oballinger/ssymmank-lamp/models/assembly/_overlap_check.scad

// OVERLAP CHECK for assembly.scad -- renders ONLY the 3D intersection of each
// close mushroom pair. Red / non-empty STL = real physical intersection;
// "top level object is empty" / 0 facets = clean. Generated by build.py.
use <../mushrooms/mushroom_simple.scad>;
MUSH_SCALE = 0.85;
MUSH = [
    [[[-0.80902, -0.58779, 0.00000, 0.00000], [-0.30902, 0.42533, 0.85065, 162.64443], [-0.50000, 0.68819, -0.52573, -100.51979], [0.00000, 0.00000, 0.00000, 1.00000]], 112.00],
    [[[0.30902, -0.87934, -0.36231, -56.33897], [-0.50000, -0.47427, 0.72462, 112.67795], [-0.80902, -0.04276, -0.58623, -91.15838], [0.00000, 0.00000, 0.00000, 1.00000]], 70.00],
    [[[1.00000, 0.00000, 0.00000, 0.00000], [0.00000, -0.81015, 0.58623, 98.13448], [0.00000, -0.58623, -0.81015, -135.61852], [0.00000, 0.00000, 0.00000, 1.00000]], 84.00],
    [[[0.30902, 0.87934, 0.36231, 56.33897], [0.50000, -0.47427, 0.72462, 112.67795], [0.80902, -0.04276, -0.58623, -91.15838], [0.00000, 0.00000, 0.00000, 1.00000]], 70.00],
    [[[-0.80902, 0.54346, 0.22392, 37.48404], [0.30902, 0.06919, 0.94854, 158.78493], [0.50000, 0.83658, -0.22392, -37.48404], [0.00000, 0.00000, 0.00000, 1.00000]], 84.00],
    [[[-0.80902, -0.54346, -0.22392, -40.14867], [-0.30902, 0.06919, 0.94854, 170.07251], [-0.50000, 0.83658, -0.22392, -40.14867], [0.00000, 0.00000, 0.00000, 1.00000]], 98.00],
    [[[0.50000, 0.68819, -0.52573, -100.51979], [-0.80902, 0.58779, 0.00000, 0.00000], [0.30902, 0.42533, 0.85065, 162.64443], [0.00000, 0.00000, 0.00000, 1.00000]], 112.00],
    [[[0.50000, 0.83658, -0.22392, -34.81940], [-0.80902, 0.54346, 0.22392, 34.81940], [0.30902, 0.06919, 0.94854, 147.49735], [0.00000, 0.00000, 0.00000, 1.00000]], 70.00],
    [[[-0.50000, 0.83658, -0.22392, -37.48404], [-0.80902, -0.54346, -0.22392, -37.48404], [-0.30902, 0.06919, 0.94854, 158.78493], [0.00000, 0.00000, 0.00000, 1.00000]], 84.00],
    [[[-0.80902, -0.04276, -0.58623, -91.15838], [0.30902, -0.87934, -0.36231, -56.33897], [-0.50000, -0.47427, 0.72462, 112.67795], [0.00000, 0.00000, 0.00000, 1.00000]], 70.00],
    [[[0.00000, -0.58623, -0.81015, -135.61852], [1.00000, 0.00000, 0.00000, 0.00000], [0.00000, -0.81015, 0.58623, 98.13448], [0.00000, 0.00000, 0.00000, 1.00000]], 84.00],
    [[[0.80902, -0.04276, -0.58623, -105.11059], [0.30902, 0.87934, 0.36231, 64.96192], [0.50000, -0.47427, 0.72462, 129.92384], [0.00000, 0.00000, 0.00000, 1.00000]], 98.00],
    [[[-0.86603, 0.50000, 0.00000, 0.00000], [-0.26287, -0.45530, 0.85065, 152.52169], [0.42533, 0.73669, 0.52573, 94.26359], [0.00000, 0.00000, 0.00000, 1.00000]], 98.00],
    [[[-1.00000, 0.00000, 0.00000, 0.00000], [0.00000, -0.81015, 0.58623, 98.13448], [0.00000, 0.58623, 0.81015, 135.61852], [0.00000, 0.00000, 0.00000, 1.00000]], 84.00],
    [[[-0.30902, -0.87934, -0.36231, -69.27339], [0.50000, -0.47427, 0.72462, 138.54678], [-0.80902, 0.04276, 0.58623, 112.08670], [0.00000, 0.00000, 0.00000, 1.00000]], 112.00],
    [[[0.80902, -0.54346, -0.22392, -34.81940], [0.30902, 0.06919, 0.94854, 147.49735], [-0.50000, -0.83658, 0.22392, 34.81940], [0.00000, 0.00000, 0.00000, 1.00000]], 70.00],
    [[[0.80902, 0.54346, 0.22392, 42.81331], [-0.30902, 0.06919, 0.94854, 181.36009], [0.50000, -0.83658, 0.22392, 42.81331], [0.00000, 0.00000, 0.00000, 1.00000]], 112.00],
    [[[-0.30902, 0.87934, 0.36231, 56.33897], [-0.50000, -0.47427, 0.72462, 112.67795], [0.80902, 0.04276, 0.58623, 91.15838], [0.00000, 0.00000, 0.00000, 1.00000]], 70.00],
    [[[0.00000, 0.85065, 0.52573, 106.77599], [1.00000, 0.00000, 0.00000, 0.00000], [0.00000, 0.52573, -0.85065, -172.76718], [0.00000, 0.00000, 0.00000, 1.00000]], 126.00],
    [[[0.00000, 0.58623, 0.81015, 125.97778], [1.00000, 0.00000, 0.00000, 0.00000], [0.00000, 0.81015, -0.58623, -91.15838], [0.00000, 0.00000, 0.00000, 1.00000]], 70.00],
    [[[-0.80902, 0.04276, 0.58623, 105.11059], [0.30902, 0.87934, 0.36231, 64.96192], [-0.50000, 0.47427, -0.72462, -129.92384], [0.00000, 0.00000, 0.00000, 1.00000]], 98.00],
    [[[-0.50000, -0.83658, 0.22392, 42.81331], [-0.80902, 0.54346, 0.22392, 42.81331], [-0.30902, -0.06919, -0.94854, -181.36009], [0.00000, 0.00000, 0.00000, 1.00000]], 112.00],
    [[[0.50000, -0.83658, 0.22392, 34.81940], [-0.80902, -0.54346, -0.22392, -34.81940], [0.30902, -0.06919, -0.94854, -147.49735], [0.00000, 0.00000, 0.00000, 1.00000]], 70.00],
    [[[0.80902, 0.04276, 0.58623, 98.13448], [0.30902, -0.87934, -0.36231, -60.65045], [0.50000, 0.47427, -0.72462, -121.30089], [0.00000, 0.00000, 0.00000, 1.00000]], 84.00],
    [[[0.50000, -0.68819, 0.52573, 106.77599], [0.80902, 0.58779, 0.00000, 0.00000], [-0.30902, 0.42533, 0.85065, 172.76718], [0.00000, 0.00000, 0.00000, 1.00000]], 126.00],
    [[[0.50000, -0.83658, 0.22392, 40.14867], [0.80902, 0.54346, 0.22392, 40.14867], [-0.30902, 0.06919, 0.94854, 170.07251], [0.00000, 0.00000, 0.00000, 1.00000]], 98.00],
    [[[0.80902, 0.04276, 0.58623, 112.08670], [-0.30902, 0.87934, 0.36231, 69.27339], [-0.50000, -0.47427, 0.72462, 138.54678], [0.00000, 0.00000, 0.00000, 1.00000]], 112.00],
    [[[0.00000, 0.58623, 0.81015, 125.97778], [-1.00000, 0.00000, 0.00000, 0.00000], [0.00000, -0.81015, 0.58623, 91.15838], [0.00000, 0.00000, 0.00000, 1.00000]], 70.00],
    [[[-0.80902, 0.04276, 0.58623, 98.13448], [-0.30902, -0.87934, -0.36231, -60.65045], [0.50000, -0.47427, 0.72462, 121.30089], [0.00000, 0.00000, 0.00000, 1.00000]], 84.00],
    [[[-0.50000, -0.83658, 0.22392, 42.81331], [0.80902, -0.54346, -0.22392, -42.81331], [0.30902, 0.06919, 0.94854, 181.36009], [0.00000, 0.00000, 0.00000, 1.00000]], 112.00],
    [[[-0.00000, -0.85065, -0.52573, -100.51979], [-1.00000, 0.00000, 0.00000, 0.00000], [0.00000, 0.52573, -0.85065, -162.64443], [0.00000, 0.00000, 0.00000, 1.00000]], 112.00],
    [[[-0.00000, -0.58623, -0.81015, -125.97778], [-1.00000, 0.00000, 0.00000, 0.00000], [0.00000, 0.81015, -0.58623, -91.15838], [0.00000, 0.00000, 0.00000, 1.00000]], 70.00],
    [[[0.80902, -0.04276, -0.58623, -98.13448], [-0.30902, -0.87934, -0.36231, -60.65045], [-0.50000, 0.47427, -0.72462, -121.30089], [0.00000, 0.00000, 0.00000, 1.00000]], 84.00],
    [[[0.50000, 0.83658, -0.22392, -40.14867], [0.80902, -0.54346, -0.22392, -40.14867], [-0.30902, -0.06919, -0.94854, -170.07251], [0.00000, 0.00000, 0.00000, 1.00000]], 98.00],
    [[[-0.50000, 0.83658, -0.22392, -45.47794], [0.80902, 0.54346, 0.22392, 45.47794], [0.30902, -0.06919, -0.94854, -192.64767], [0.00000, 0.00000, 0.00000, 1.00000]], 126.00],
    [[[-0.80902, -0.04276, -0.58623, -105.11059], [-0.30902, 0.87934, 0.36231, 64.96192], [0.50000, 0.47427, -0.72462, -129.92384], [0.00000, 0.00000, 0.00000, 1.00000]], 98.00],
    [[[0.80902, 0.58779, 0.00000, 0.00000], [0.30902, -0.42533, -0.85065, -172.76718], [-0.50000, 0.68819, -0.52573, -106.77599], [0.00000, 0.00000, 0.00000, 1.00000]], 126.00],
    [[[-0.30902, 0.87934, 0.36231, 64.96192], [0.50000, 0.47427, -0.72462, -129.92384], [-0.80902, -0.04276, -0.58623, -105.11059], [0.00000, 0.00000, 0.00000, 1.00000]], 98.00],
    [[[-1.00000, 0.00000, 0.00000, 0.00000], [0.00000, 0.81015, -0.58623, -112.08670], [-0.00000, -0.58623, -0.81015, -154.90001], [0.00000, 0.00000, 0.00000, 1.00000]], 112.00],
    [[[-0.30902, -0.87934, -0.36231, -56.33897], [-0.50000, 0.47427, -0.72462, -112.67795], [0.80902, -0.04276, -0.58623, -91.15838], [0.00000, 0.00000, 0.00000, 1.00000]], 70.00],
    [[[0.80902, -0.54346, -0.22392, -37.48404], [-0.30902, -0.06919, -0.94854, -158.78493], [0.50000, 0.83658, -0.22392, -37.48404], [0.00000, 0.00000, 0.00000, 1.00000]], 84.00],
    [[[0.80902, 0.54346, 0.22392, 42.81331], [0.30902, -0.06919, -0.94854, -181.36009], [-0.50000, 0.83658, -0.22392, -42.81331], [0.00000, 0.00000, 0.00000, 1.00000]], 112.00],
    [[[0.86603, -0.50000, 0.00000, 0.00000], [0.26287, 0.45530, -0.85065, -142.39895], [0.42533, 0.73669, 0.52573, 88.00739], [0.00000, 0.00000, 0.00000, 1.00000]], 84.00],
    [[[1.00000, 0.00000, 0.00000, 0.00000], [0.00000, 0.81015, -0.58623, -105.11059], [0.00000, 0.58623, 0.81015, 145.25926], [0.00000, 0.00000, 0.00000, 1.00000]], 98.00],
    [[[0.30902, 0.87934, 0.36231, 56.33897], [-0.50000, 0.47427, -0.72462, -112.67795], [-0.80902, 0.04276, 0.58623, 91.15838], [0.00000, 0.00000, 0.00000, 1.00000]], 70.00],
    [[[-0.80902, 0.54346, 0.22392, 40.14867], [-0.30902, -0.06919, -0.94854, -170.07251], [-0.50000, -0.83658, 0.22392, 40.14867], [0.00000, 0.00000, 0.00000, 1.00000]], 98.00],
    [[[-0.80902, -0.54346, -0.22392, -34.81940], [0.30902, -0.06919, -0.94854, -147.49735], [0.50000, -0.83658, 0.22392, 34.81940], [0.00000, 0.00000, 0.00000, 1.00000]], 70.00],
    [[[0.30902, -0.87934, -0.36231, -69.27339], [0.50000, 0.47427, -0.72462, -138.54678], [0.80902, 0.04276, 0.58623, 112.08670], [0.00000, 0.00000, 0.00000, 1.00000]], 112.00],
    [[[0.50000, 0.16246, 0.85065, 132.27620], [-0.80902, -0.26287, 0.52573, 81.75119], [0.30902, -0.95106, 0.00000, 0.00000], [0.00000, 0.00000, 0.00000, 1.00000]], 70.00],
    [[[-0.50000, -0.47427, 0.72462, 121.30089], [0.80902, 0.04276, 0.58623, 98.13448], [-0.30902, 0.87934, 0.36231, 60.65045], [0.00000, 0.00000, 0.00000, 1.00000]], 84.00],
    [[[0.00000, -0.81015, 0.58623, 105.11059], [0.00000, 0.58623, 0.81015, 145.25926], [-1.00000, 0.00000, 0.00000, 0.00000], [0.00000, 0.00000, 0.00000, 1.00000]], 98.00],
    [[[0.50000, -0.47427, 0.72462, 138.54678], [-0.80902, 0.04276, 0.58623, 112.08670], [-0.30902, -0.87934, -0.36231, -69.27339], [0.00000, 0.00000, 0.00000, 1.00000]], 112.00],
    [[[0.30902, 0.06919, 0.94854, 158.78493], [-0.50000, -0.83658, 0.22392, 37.48404], [0.80902, -0.54346, -0.22392, -37.48404], [0.00000, 0.00000, 0.00000, 1.00000]], 84.00],
    [[[-0.30902, 0.06919, 0.94854, 170.07251], [0.50000, -0.83658, 0.22392, 40.14867], [0.80902, 0.54346, 0.22392, 40.14867], [0.00000, 0.00000, 0.00000, 1.00000]], 98.00],
    [[[0.51424, -0.10931, -0.85065, -132.27620], [-0.83206, 0.17686, -0.52573, -81.75119], [0.20791, 0.97815, 0.00000, 0.00000], [0.00000, 0.00000, 0.00000, 1.00000]], 70.00],
    [[[0.00000, 0.81015, -0.58623, -105.11059], [-0.00000, -0.58623, -0.81015, -145.25926], [-1.00000, 0.00000, 0.00000, 0.00000], [0.00000, 0.00000, 0.00000, 1.00000]], 98.00],
    [[[-0.50000, 0.47427, -0.72462, -138.54678], [0.80902, -0.04276, -0.58623, -112.08670], [-0.30902, -0.87934, -0.36231, -69.27339], [0.00000, 0.00000, 0.00000, 1.00000]], 112.00],
    [[[-0.30902, -0.06919, -0.94854, -170.07251], [0.50000, 0.83658, -0.22392, -40.14867], [0.80902, -0.54346, -0.22392, -40.14867], [0.00000, 0.00000, 0.00000, 1.00000]], 98.00],
    [[[0.30902, -0.06919, -0.94854, -181.36009], [-0.50000, 0.83658, -0.22392, -42.81331], [0.80902, 0.54346, 0.22392, 42.81331], [0.00000, 0.00000, 0.00000, 1.00000]], 112.00],
    [[[0.50000, 0.47427, -0.72462, -147.16972], [-0.80902, -0.04276, -0.58623, -119.06281], [-0.30902, 0.87934, 0.36231, 73.58486], [0.00000, 0.00000, 0.00000, 1.00000]], 126.00],
    [[[-0.50000, 0.16246, -0.85065, -152.52169], [-0.80902, 0.26287, 0.52573, 94.26359], [0.30902, 0.95106, 0.00000, 0.00000], [0.00000, 0.00000, 0.00000, 1.00000]], 98.00],
    [[[-0.50000, 0.47427, -0.72462, -147.16972], [-0.80902, 0.04276, 0.58623, 119.06281], [0.30902, 0.87934, 0.36231, 73.58486], [0.00000, 0.00000, 0.00000, 1.00000]], 126.00],
    [[[-0.30902, -0.06919, -0.94854, -147.49735], [-0.50000, -0.83658, 0.22392, 34.81940], [-0.80902, 0.54346, 0.22392, 34.81940], [0.00000, 0.00000, 0.00000, 1.00000]], 70.00],
    [[[0.30902, -0.06919, -0.94854, -158.78493], [0.50000, -0.83658, 0.22392, 37.48404], [-0.80902, -0.54346, -0.22392, -37.48404], [0.00000, 0.00000, 0.00000, 1.00000]], 84.00],
    [[[0.50000, 0.47427, -0.72462, -138.54678], [0.80902, 0.04276, 0.58623, 112.08670], [0.30902, -0.87934, -0.36231, -69.27339], [0.00000, 0.00000, 0.00000, 1.00000]], 112.00],
    [[[0.00000, 0.81015, -0.58623, -98.13448], [0.00000, 0.58623, 0.81015, 135.61852], [1.00000, 0.00000, 0.00000, 0.00000], [0.00000, 0.00000, 0.00000, 1.00000]], 84.00],
    [[[0.35178, -0.39069, 0.85065, 132.27620], [0.56920, -0.63216, -0.52573, -81.75119], [0.74314, 0.66913, 0.00000, 0.00000], [0.00000, 0.00000, 0.00000, 1.00000]], 70.00],
    [[[0.30902, 0.06919, 0.94854, 192.64767], [0.50000, 0.83658, -0.22392, -45.47794], [-0.80902, 0.54346, 0.22392, 45.47794], [0.00000, 0.00000, 0.00000, 1.00000]], 126.00],
    [[[-0.30902, 0.06919, 0.94854, 181.36009], [-0.50000, 0.83658, -0.22392, -42.81331], [-0.80902, -0.54346, -0.22392, -42.81331], [0.00000, 0.00000, 0.00000, 1.00000]], 112.00],
    [[[-0.50000, -0.47427, 0.72462, 147.16972], [-0.80902, -0.04276, -0.58623, -119.06281], [0.30902, -0.87934, -0.36231, -73.58486], [0.00000, 0.00000, 0.00000, 1.00000]], 126.00],
    [[[0.00000, -0.81015, 0.58623, 98.13448], [0.00000, -0.58623, -0.81015, -135.61852], [1.00000, 0.00000, 0.00000, 0.00000], [0.00000, 0.00000, 0.00000, 1.00000]], 84.00],
    [[[0.50000, -0.47427, 0.72462, 138.54678], [0.80902, -0.04276, -0.58623, -112.08670], [0.30902, 0.87934, 0.36231, 69.27339], [0.00000, 0.00000, 0.00000, 1.00000]], 112.00]
];
PAIRS = [
    [0, 5],
    [1, 2],
    [1, 65],
    [2, 3],
    [2, 20],
    [2, 35],
    [3, 4],
    [4, 5],
    [4, 15],
    [6, 11],
    [7, 8],
    [7, 13],
    [8, 9],
    [8, 25],
    [9, 10],
    [10, 11],
    [10, 62],
    [11, 13],
    [12, 13],
    [12, 14],
    [12, 15],
    [12, 16],
    [12, 17],
    [13, 17],
    [15, 65],
    [17, 49],
    [19, 23],
    [19, 52],
    [20, 52],
    [22, 23],
    [27, 28],
    [27, 49],
    [28, 43],
    [28, 44],
    [30, 33],
    [30, 34],
    [30, 35],
    [31, 32],
    [31, 63],
    [32, 33],
    [32, 39],
    [32, 57],
    [35, 63],
    [37, 70],
    [39, 40],
    [40, 45],
    [40, 46],
    [42, 43],
    [42, 44],
    [42, 45],
    [42, 46],
    [42, 47],
    [44, 70],
    [48, 49],
    [48, 50],
    [48, 51],
    [48, 52],
    [48, 53],
    [49, 50],
    [49, 53],
    [52, 53],
    [54, 55],
    [54, 56],
    [54, 57],
    [54, 58],
    [54, 59],
    [60, 61],
    [60, 62],
    [60, 63],
    [60, 64],
    [60, 65],
    [62, 63],
    [66, 67],
    [66, 68],
    [66, 69],
    [66, 70],
    [66, 71]
];
module one(i){ multmatrix(MUSH[i][0]) scale(MUSH_SCALE) mushroom(MUSH[i][1], paint=false); }
color("red") for (p = PAIRS) intersection(){ one(p[0]); one(p[1]); }
