oballinger/ssymmank-lamp/models/frame/stars_assembly.scad

// Ssymmank lamp -- FIT CHECK: 12 star tiles + 60 connectors = full frame.
// Modules/params (incl. the kink welds) come from star.scad, so edits there
// propagate here -- this file only carries the world placements.

include <star.scad>
SHOW_STAR = false;   // library mode: don't draw the lone star tile

PLACE_M = [
    [[-0.58779, 0.80902, 0.00000, 0.00000], [0.42533, 0.30902, 0.85065, 85.06508], [0.68819, 0.50000, -0.52573, -52.57311], [0.00000, 0.00000, 0.00000, 1.00000]],
    [[0.68819, -0.50000, -0.52573, -52.57311], [0.58779, 0.80902, 0.00000, 0.00000], [0.42533, -0.30902, 0.85065, 85.06508], [0.00000, 0.00000, 0.00000, 1.00000]],
    [[0.00000, 1.00000, 0.00000, 0.00000], [-0.52573, 0.00000, 0.85065, 85.06508], [0.85065, -0.00000, 0.52573, 52.57311], [0.00000, 0.00000, 0.00000, 1.00000]],
    [[0.85065, 0.00000, 0.52573, 52.57311], [0.00000, -1.00000, 0.00000, 0.00000], [0.52573, 0.00000, -0.85065, -85.06508], [0.00000, 0.00000, 0.00000, 1.00000]],
    [[-0.68819, -0.50000, 0.52573, 52.57311], [0.58779, -0.80902, 0.00000, 0.00000], [0.42533, 0.30902, 0.85065, 85.06508], [0.00000, 0.00000, 0.00000, 1.00000]],
    [[-0.85065, 0.00000, -0.52573, -52.57311], [0.00000, 1.00000, 0.00000, 0.00000], [0.52573, 0.00000, -0.85065, -85.06508], [0.00000, 0.00000, 0.00000, 1.00000]],
    [[0.58779, -0.80902, 0.00000, 0.00000], [-0.42533, -0.30902, -0.85065, -85.06508], [0.68819, 0.50000, -0.52573, -52.57311], [0.00000, 0.00000, 0.00000, 1.00000]],
    [[0.00000, -1.00000, 0.00000, 0.00000], [0.52573, 0.00000, -0.85065, -85.06508], [0.85065, 0.00000, 0.52573, 52.57311], [0.00000, 0.00000, 0.00000, 1.00000]],
    [[-0.16246, 0.50000, 0.85065, 85.06508], [0.26287, -0.80902, 0.52573, 52.57311], [0.95106, 0.30902, 0.00000, 0.00000], [0.00000, 0.00000, 0.00000, 1.00000]],
    [[0.16246, -0.50000, -0.85065, -85.06508], [-0.26287, 0.80902, -0.52573, -52.57311], [0.95106, 0.30902, 0.00000, 0.00000], [0.00000, 0.00000, 0.00000, 1.00000]],
    [[0.16246, 0.50000, -0.85065, -85.06508], [0.26287, 0.80902, 0.52573, 52.57311], [0.95106, -0.30902, 0.00000, 0.00000], [0.00000, 0.00000, 0.00000, 1.00000]],
    [[-0.16246, -0.50000, 0.85065, 85.06508], [-0.26287, -0.80902, -0.52573, -52.57311], [0.95106, -0.30902, 0.00000, 0.00000], [0.00000, 0.00000, 0.00000, 1.00000]]
];
CONN_M = [
    [[0.00000, 0.22975, -0.97325, -94.85360], [1.00000, 0.00000, 0.00000, 0.00000], [0.00000, -0.97325, -0.22975, -22.39190], [0.00000, 0.00000, 0.00000, 1.00000]],
    [[0.30902, 0.30075, -0.90225, -87.93412], [0.50000, -0.85837, -0.11488, -11.19595], [-0.80902, -0.41563, -0.41563, -40.50732], [0.00000, 0.00000, 0.00000, 1.00000]],
    [[0.00000, -0.22975, -0.97325, -94.85360], [1.00000, 0.00000, 0.00000, 0.00000], [0.00000, -0.97325, 0.22975, 22.39190], [0.00000, 0.00000, 0.00000, 1.00000]],
    [[0.30902, -0.30075, -0.90225, -87.93412], [0.50000, 0.85837, -0.11488, -11.19595], [0.80902, -0.41563, 0.41563, 40.50732], [0.00000, 0.00000, 0.00000, 1.00000]],
    [[0.30902, -0.30075, -0.90225, -87.93412], [-0.50000, -0.85837, 0.11488, 11.19595], [-0.80902, 0.41563, -0.41563, -40.50732], [0.00000, 0.00000, 0.00000, 1.00000]],
    [[0.30902, 0.30075, -0.90225, -87.93412], [-0.50000, 0.85837, 0.11488, 11.19595], [0.80902, 0.41563, 0.41563, 40.50732], [0.00000, 0.00000, 0.00000, 1.00000]],
    [[0.30902, 0.67250, -0.67250, -65.54223], [0.50000, -0.71638, -0.48662, -47.42680], [-0.80902, -0.18587, -0.55762, -54.34628], [0.00000, 0.00000, 0.00000, 1.00000]],
    [[0.80902, 0.18587, -0.55762, -54.34628], [-0.30902, -0.67250, -0.67250, -65.54223], [-0.50000, 0.71638, -0.48662, -47.42680], [0.00000, 0.00000, 0.00000, 1.00000]],
    [[0.30902, -0.67250, -0.67250, -65.54223], [0.50000, 0.71638, -0.48662, -47.42680], [0.80902, -0.18587, 0.55762, 54.34628], [0.00000, 0.00000, 0.00000, 1.00000]],
    [[0.80902, -0.18587, -0.55762, -54.34628], [-0.30902, 0.67250, -0.67250, -65.54223], [0.50000, 0.71638, 0.48662, 47.42680], [0.00000, 0.00000, 0.00000, 1.00000]],
    [[0.30902, -0.67250, -0.67250, -65.54223], [-0.50000, -0.71638, 0.48662, 47.42680], [-0.80902, 0.18587, -0.55762, -54.34628], [0.00000, 0.00000, 0.00000, 1.00000]],
    [[0.80902, -0.18587, -0.55762, -54.34628], [0.30902, -0.67250, 0.67250, 65.54223], [-0.50000, -0.71638, -0.48662, -47.42680], [0.00000, 0.00000, 0.00000, 1.00000]],
    [[0.30902, 0.67250, -0.67250, -65.54223], [-0.50000, 0.71638, 0.48662, 47.42680], [0.80902, 0.18587, 0.55762, 54.34628], [0.00000, 0.00000, 0.00000, 1.00000]],
    [[0.80902, 0.18587, -0.55762, -54.34628], [0.30902, 0.67250, 0.67250, 65.54223], [0.50000, -0.71638, 0.48662, 47.42680], [0.00000, 0.00000, 0.00000, 1.00000]],
    [[0.80902, 0.41563, -0.41563, -40.50732], [-0.30902, -0.30075, -0.90225, -87.93412], [-0.50000, 0.85837, -0.11488, -11.19595], [0.00000, 0.00000, 0.00000, 1.00000]],
    [[0.80902, -0.41563, -0.41563, -40.50732], [-0.30902, 0.30075, -0.90225, -87.93412], [0.50000, 0.85837, 0.11488, 11.19595], [0.00000, 0.00000, 0.00000, 1.00000]],
    [[0.50000, -0.71638, -0.48662, -47.42680], [-0.80902, -0.18587, -0.55762, -54.34628], [0.30902, 0.67250, -0.67250, -65.54223], [0.00000, 0.00000, 0.00000, 1.00000]],
    [[0.50000, 0.71638, -0.48662, -47.42680], [-0.80902, 0.18587, -0.55762, -54.34628], [-0.30902, 0.67250, 0.67250, 65.54223], [0.00000, 0.00000, 0.00000, 1.00000]],
    [[0.50000, 0.71638, -0.48662, -47.42680], [0.80902, -0.18587, 0.55762, 54.34628], [0.30902, -0.67250, -0.67250, -65.54223], [0.00000, 0.00000, 0.00000, 1.00000]],
    [[0.50000, -0.71638, -0.48662, -47.42680], [0.80902, 0.18587, 0.55762, 54.34628], [-0.30902, -0.67250, 0.67250, 65.54223], [0.00000, 0.00000, 0.00000, 1.00000]],
    [[0.80902, -0.41563, -0.41563, -40.50732], [0.30902, -0.30075, 0.90225, 87.93412], [-0.50000, -0.85837, -0.11488, -11.19595], [0.00000, 0.00000, 0.00000, 1.00000]],
    [[0.80902, 0.41563, -0.41563, -40.50732], [0.30902, 0.30075, 0.90225, 87.93412], [0.50000, -0.85837, 0.11488, 11.19595], [0.00000, 0.00000, 0.00000, 1.00000]],
    [[0.00000, -0.97325, -0.22975, -22.39190], [0.00000, 0.22975, -0.97325, -94.85360], [1.00000, 0.00000, 0.00000, 0.00000], [0.00000, 0.00000, 0.00000, 1.00000]],
    [[0.50000, -0.85837, -0.11488, -11.19595], [-0.80902, -0.41563, -0.41563, -40.50732], [0.30902, 0.30075, -0.90225, -87.93412], [0.00000, 0.00000, 0.00000, 1.00000]],
    [[1.00000, 0.00000, 0.00000, 0.00000], [0.00000, -0.97325, -0.22975, -22.39190], [0.00000, 0.22975, -0.97325, -94.85360], [0.00000, 0.00000, 0.00000, 1.00000]],
    [[0.50000, 0.85837, -0.11488, -11.19595], [-0.80902, 0.41563, -0.41563, -40.50732], [-0.30902, 0.30075, 0.90225, 87.93412], [0.00000, 0.00000, 0.00000, 1.00000]],
    [[1.00000, -0.00000, 0.00000, 0.00000], [0.00000, 0.97325, -0.22975, -22.39190], [0.00000, 0.22975, 0.97325, 94.85360], [0.00000, 0.00000, 0.00000, 1.00000]],
    [[0.50000, 0.85837, -0.11488, -11.19595], [0.80902, -0.41563, 0.41563, 40.50732], [0.30902, -0.30075, -0.90225, -87.93412], [0.00000, 0.00000, 0.00000, 1.00000]],
    [[1.00000, 0.00000, 0.00000, 0.00000], [0.00000, -0.97325, 0.22975, 22.39190], [0.00000, -0.22975, -0.97325, -94.85360], [0.00000, 0.00000, 0.00000, 1.00000]],
    [[0.50000, -0.85837, -0.11488, -11.19595], [0.80902, 0.41563, 0.41563, 40.50732], [-0.30902, -0.30075, 0.90225, 87.93412], [0.00000, 0.00000, 0.00000, 1.00000]],
    [[1.00000, 0.00000, 0.00000, 0.00000], [0.00000, 0.97325, 0.22975, 22.39190], [0.00000, -0.22975, 0.97325, 94.85360], [0.00000, 0.00000, 0.00000, 1.00000]],
    [[0.00000, 0.97325, -0.22975, -22.39190], [0.00000, 0.22975, 0.97325, 94.85360], [1.00000, -0.00000, 0.00000, 0.00000], [0.00000, 0.00000, 0.00000, 1.00000]],
    [[0.50000, 0.85837, 0.11488, 11.19595], [0.80902, -0.41563, -0.41563, -40.50732], [-0.30902, 0.30075, -0.90225, -87.93412], [0.00000, 0.00000, 0.00000, 1.00000]],
    [[0.50000, -0.85837, 0.11488, 11.19595], [0.80902, 0.41563, -0.41563, -40.50732], [0.30902, 0.30075, 0.90225, 87.93412], [0.00000, 0.00000, 0.00000, 1.00000]],
    [[0.50000, -0.85837, 0.11488, 11.19595], [-0.80902, -0.41563, 0.41563, 40.50732], [-0.30902, -0.30075, -0.90225, -87.93412], [0.00000, 0.00000, 0.00000, 1.00000]],
    [[0.50000, 0.85837, 0.11488, 11.19595], [-0.80902, 0.41563, 0.41563, 40.50732], [0.30902, -0.30075, 0.90225, 87.93412], [0.00000, 0.00000, 0.00000, 1.00000]],
    [[0.00000, -0.97325, 0.22975, 22.39190], [0.00000, -0.22975, -0.97325, -94.85360], [1.00000, 0.00000, 0.00000, 0.00000], [0.00000, 0.00000, 0.00000, 1.00000]],
    [[0.80902, -0.41563, 0.41563, 40.50732], [0.30902, -0.30075, -0.90225, -87.93412], [0.50000, 0.85837, -0.11488, -11.19595], [0.00000, 0.00000, 0.00000, 1.00000]],
    [[0.80902, 0.41563, 0.41563, 40.50732], [0.30902, 0.30075, -0.90225, -87.93412], [-0.50000, 0.85837, 0.11488, 11.19595], [0.00000, 0.00000, 0.00000, 1.00000]],
    [[0.00000, 0.97325, 0.22975, 22.39190], [0.00000, -0.22975, 0.97325, 94.85360], [1.00000, 0.00000, 0.00000, 0.00000], [0.00000, 0.00000, 0.00000, 1.00000]],
    [[0.80902, 0.41563, 0.41563, 40.50732], [-0.30902, -0.30075, 0.90225, 87.93412], [0.50000, -0.85837, -0.11488, -11.19595], [0.00000, 0.00000, 0.00000, 1.00000]],
    [[0.80902, -0.41563, 0.41563, 40.50732], [-0.30902, 0.30075, 0.90225, 87.93412], [-0.50000, -0.85837, 0.11488, 11.19595], [0.00000, 0.00000, 0.00000, 1.00000]],
    [[0.50000, 0.71638, 0.48662, 47.42680], [0.80902, -0.18587, -0.55762, -54.34628], [-0.30902, 0.67250, -0.67250, -65.54223], [0.00000, 0.00000, 0.00000, 1.00000]],
    [[0.80902, -0.18587, 0.55762, 54.34628], [0.30902, -0.67250, -0.67250, -65.54223], [0.50000, 0.71638, -0.48662, -47.42680], [0.00000, 0.00000, 0.00000, 1.00000]],
    [[0.50000, -0.71638, 0.48662, 47.42680], [0.80902, 0.18587, -0.55762, -54.34628], [0.30902, 0.67250, 0.67250, 65.54223], [0.00000, 0.00000, 0.00000, 1.00000]],
    [[0.80902, 0.18587, 0.55762, 54.34628], [0.30902, 0.67250, -0.67250, -65.54223], [-0.50000, 0.71638, 0.48662, 47.42680], [0.00000, 0.00000, 0.00000, 1.00000]],
    [[0.50000, -0.71638, 0.48662, 47.42680], [-0.80902, -0.18587, 0.55762, 54.34628], [-0.30902, -0.67250, -0.67250, -65.54223], [0.00000, 0.00000, 0.00000, 1.00000]],
    [[0.80902, 0.18587, 0.55762, 54.34628], [-0.30902, -0.67250, 0.67250, 65.54223], [0.50000, -0.71638, -0.48662, -47.42680], [0.00000, 0.00000, 0.00000, 1.00000]],
    [[0.50000, 0.71638, 0.48662, 47.42680], [-0.80902, 0.18587, 0.55762, 54.34628], [0.30902, -0.67250, 0.67250, 65.54223], [0.00000, 0.00000, 0.00000, 1.00000]],
    [[0.80902, -0.18587, 0.55762, 54.34628], [-0.30902, 0.67250, 0.67250, 65.54223], [-0.50000, -0.71638, 0.48662, 47.42680], [0.00000, 0.00000, 0.00000, 1.00000]],
    [[0.30902, -0.67250, 0.67250, 65.54223], [-0.50000, -0.71638, -0.48662, -47.42680], [0.80902, -0.18587, -0.55762, -54.34628], [0.00000, 0.00000, 0.00000, 1.00000]],
    [[0.30902, 0.67250, 0.67250, 65.54223], [-0.50000, 0.71638, -0.48662, -47.42680], [-0.80902, -0.18587, 0.55762, 54.34628], [0.00000, 0.00000, 0.00000, 1.00000]],
    [[0.30902, 0.67250, 0.67250, 65.54223], [0.50000, -0.71638, 0.48662, 47.42680], [0.80902, 0.18587, -0.55762, -54.34628], [0.00000, 0.00000, 0.00000, 1.00000]],
    [[0.30902, -0.67250, 0.67250, 65.54223], [0.50000, 0.71638, 0.48662, 47.42680], [-0.80902, 0.18587, 0.55762, 54.34628], [0.00000, 0.00000, 0.00000, 1.00000]],
    [[0.30902, -0.30075, 0.90225, 87.93412], [-0.50000, -0.85837, -0.11488, -11.19595], [0.80902, -0.41563, -0.41563, -40.50732], [0.00000, 0.00000, 0.00000, 1.00000]],
    [[0.30902, 0.30075, 0.90225, 87.93412], [0.50000, -0.85837, 0.11488, 11.19595], [0.80902, 0.41563, -0.41563, -40.50732], [0.00000, 0.00000, 0.00000, 1.00000]],
    [[0.30902, 0.30075, 0.90225, 87.93412], [-0.50000, 0.85837, -0.11488, -11.19595], [-0.80902, -0.41563, 0.41563, 40.50732], [0.00000, 0.00000, 0.00000, 1.00000]],
    [[0.30902, -0.30075, 0.90225, 87.93412], [0.50000, 0.85837, 0.11488, 11.19595], [-0.80902, 0.41563, 0.41563, 40.50732], [0.00000, 0.00000, 0.00000, 1.00000]],
    [[0.00000, 0.22975, 0.97325, 94.85360], [1.00000, -0.00000, 0.00000, 0.00000], [0.00000, 0.97325, -0.22975, -22.39190], [0.00000, 0.00000, 0.00000, 1.00000]],
    [[0.00000, -0.22975, 0.97325, 94.85360], [1.00000, 0.00000, 0.00000, 0.00000], [0.00000, 0.97325, 0.22975, 22.39190], [0.00000, 0.00000, 0.00000, 1.00000]]
];

// The whole frame as one reusable module: 12 star tiles + 60 connectors.
// assembly.scad includes this file and calls frame() (with SHOW_FRAME=false).
module frame() {
    color("#4F86C6") multmatrix(PLACE_M[0]) star();
    color("#C64F4F") multmatrix(PLACE_M[1]) star();
    color("#4FC686") multmatrix(PLACE_M[2]) star();
    color("#C6A14F") multmatrix(PLACE_M[3]) star();
    color("#864FC6") multmatrix(PLACE_M[4]) star();
    color("#4FC6C6") multmatrix(PLACE_M[5]) star();
    color("#C64F86") multmatrix(PLACE_M[6]) star();
    color("#86C64F") multmatrix(PLACE_M[7]) star();
    color("#C6864F") multmatrix(PLACE_M[8]) star();
    color("#4F4FC6") multmatrix(PLACE_M[9]) star();
    color("#C6C64F") multmatrix(PLACE_M[10]) star();
    color("#9C9C9C") multmatrix(PLACE_M[11]) star();
    color("#BBBBBB") for (m = CONN_M) multmatrix(m) connector();
}

SHOW_FRAME = true;        // set false by includers (assembly.scad) that draw it themselves
if (SHOW_FRAME) frame();
