oballinger/ssymmank-lamp/models/mushrooms/mushroom_large.scad

// Ssymmank mushroom -- LARGE stem (simplified, fast-loading).
// Includes the simplified core and overrides only the stem length.
include <mushroom_simple.scad>;
STEM_LEN = 98;   // shell 3 of the 5 shingled shells
